kiu/rfm12trx/media/rfm12trx-edge.jpg

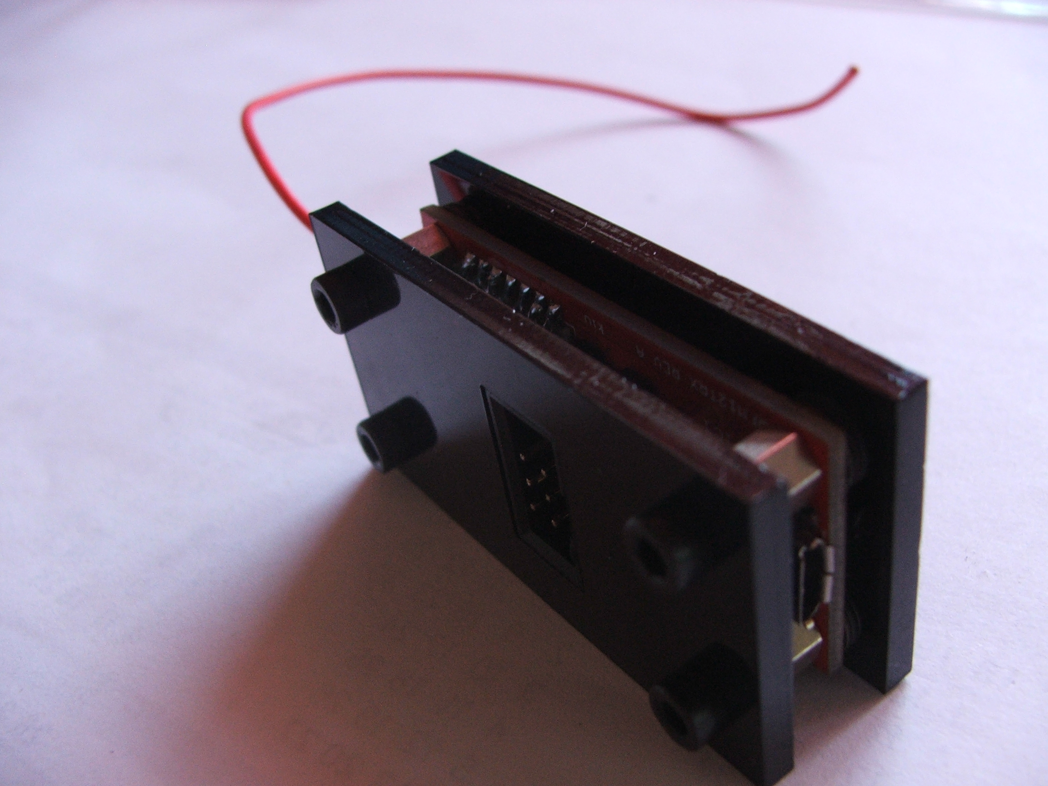
media/rfm12trx-edge.jpg
