kiu/rfm12trx/media/rfm12trx-terminal.png

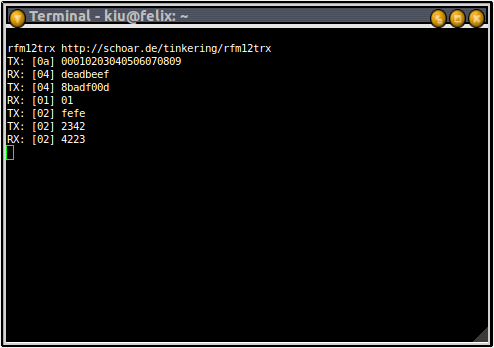
media/rfm12trx-terminal.png
